omega9380/WildCatMFD/screen dimensions from Lebula/7inch raspberry pi monitor dimensions -back view 02.pdf

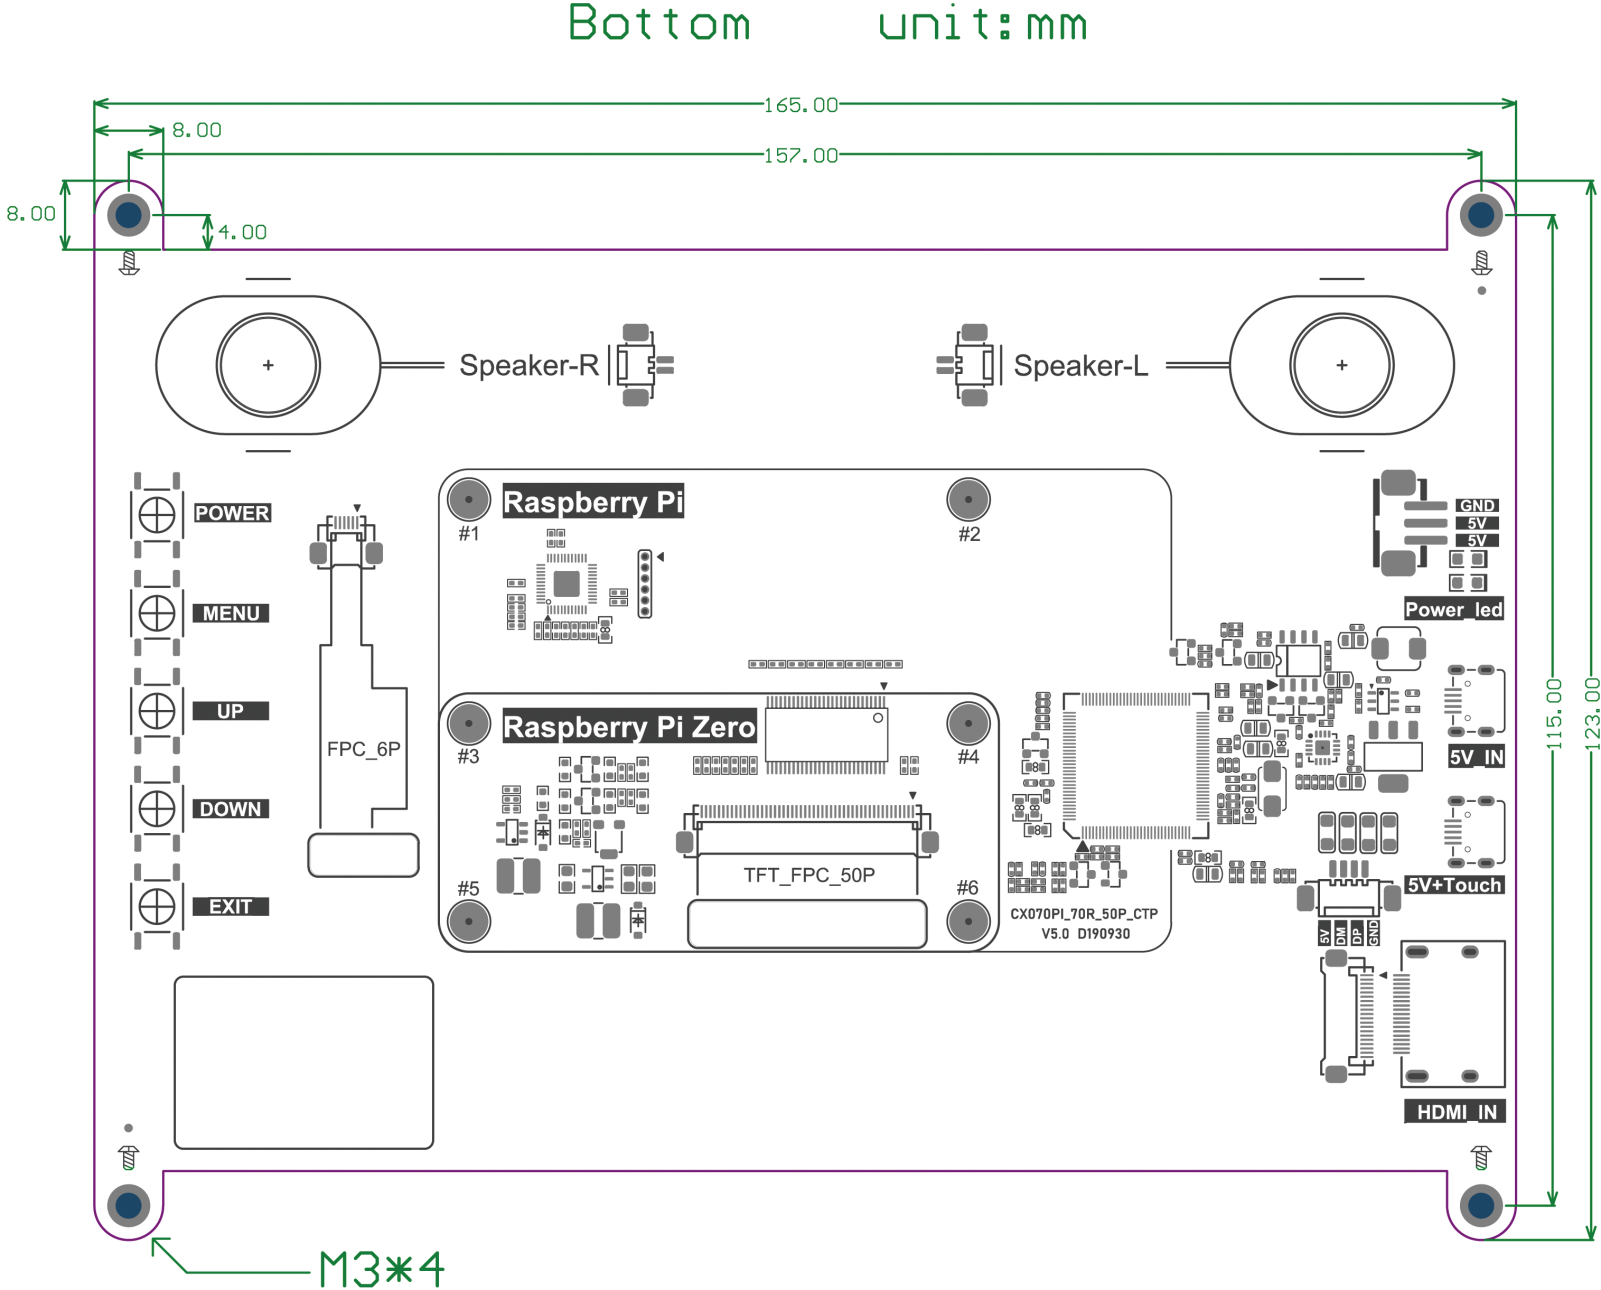
[picture p16: page 1]
