omega9380/WildCatMFD/screen dimensions from Lebula/7inch raspberry pi monitor dimensions -front view02.pdf

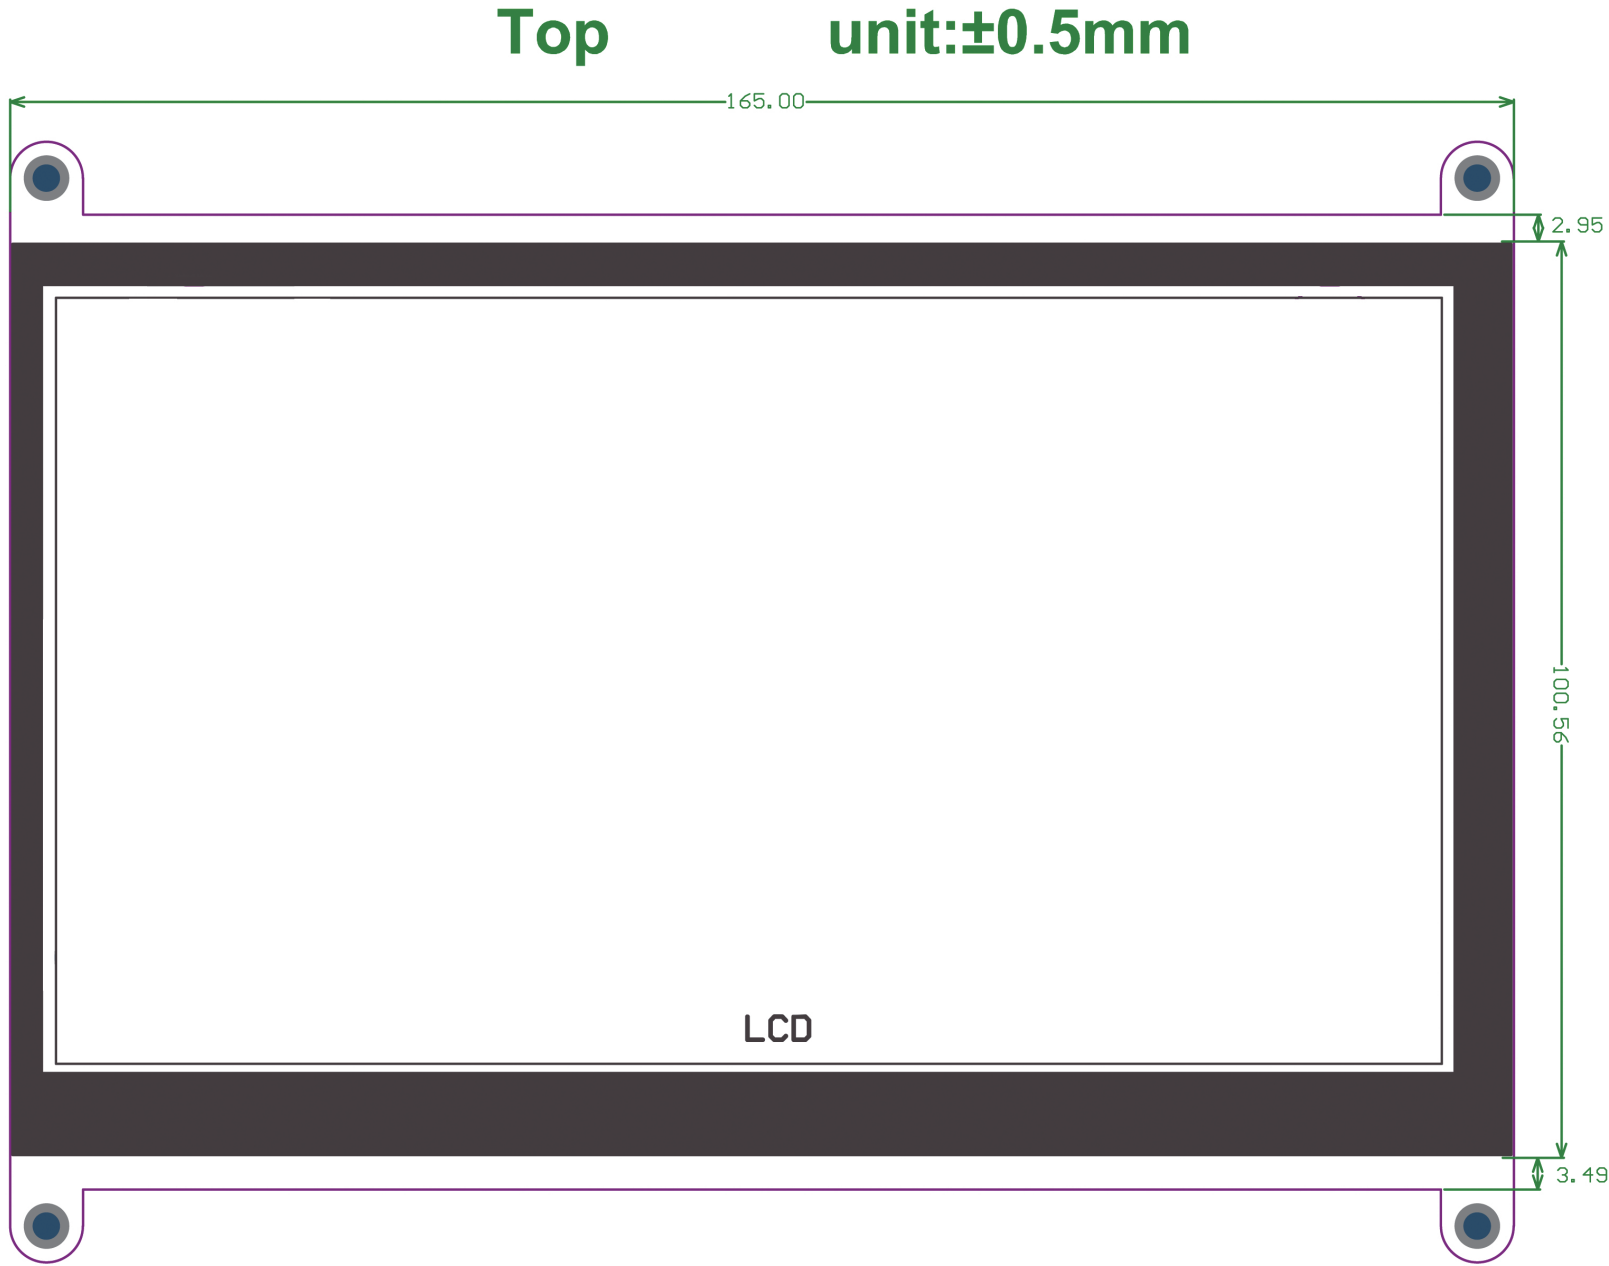
[picture p17: page 1]
