omega9380/WildCatMFD/wildcatmfd_kicad/WILDCAT_BOARD.PDF

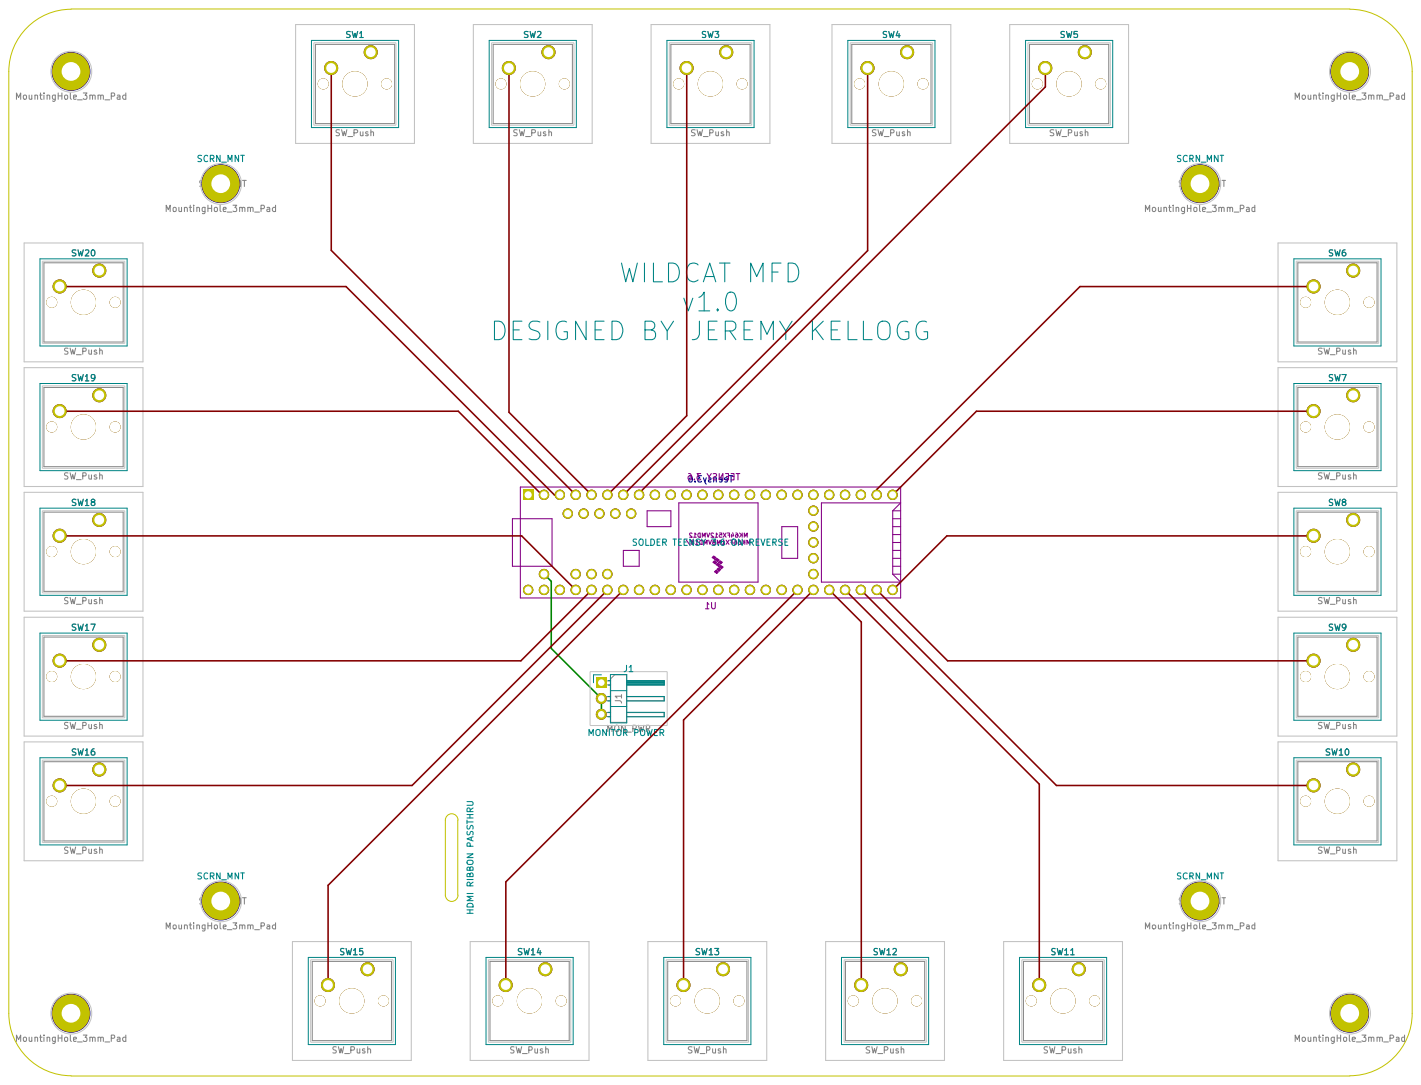
[picture p18: page 1]
